iamjadhav/mobile_robot_arm/meshes/picking_arm.STL

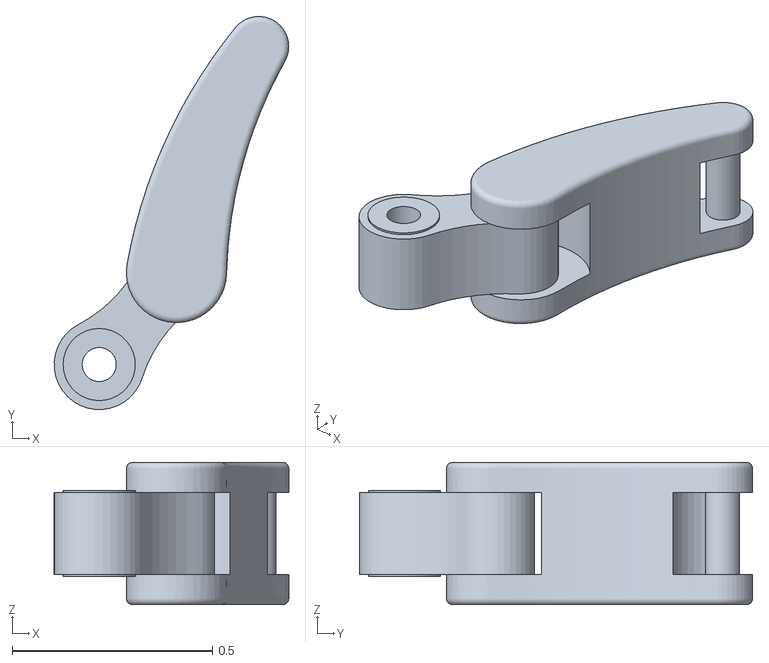
[picture p27: CAD file, 2021-12-11]
meshes/picking_arm.STL
0.585 x 0.981 x 0.355
