iamjadhav/mobile_robot_arm/solidworks_assembly/trolley.SLDPRT

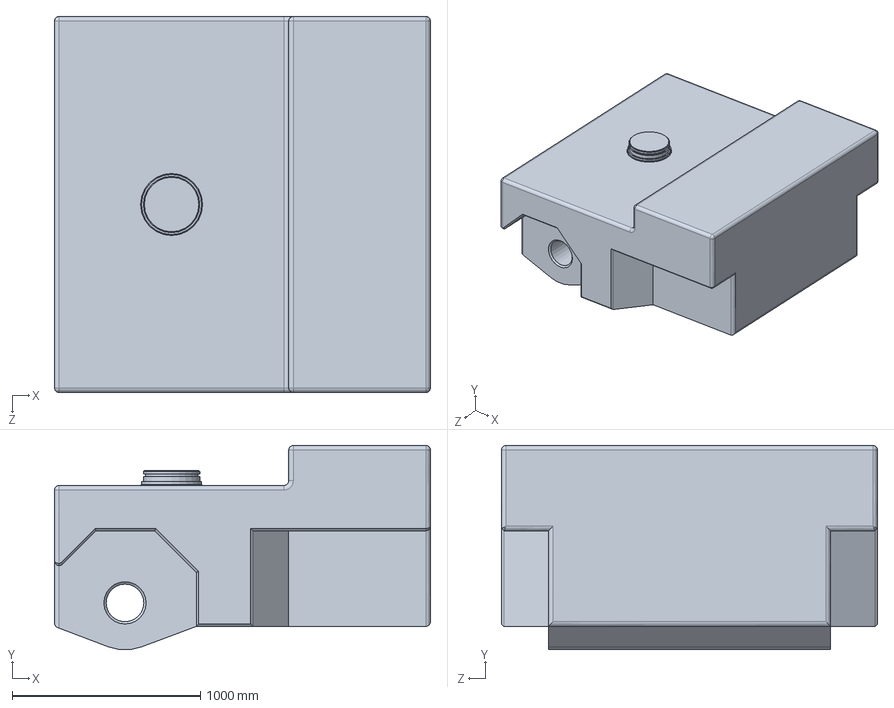
[picture p28: CAD file, 2021-12-11]
solidworks_assembly/trolley.SLDPRT
2000.0 x 1085.8 x 2000.0 mm
