iamjadhav/mobile_robot_arm/meshes/front_right_wheel.STL

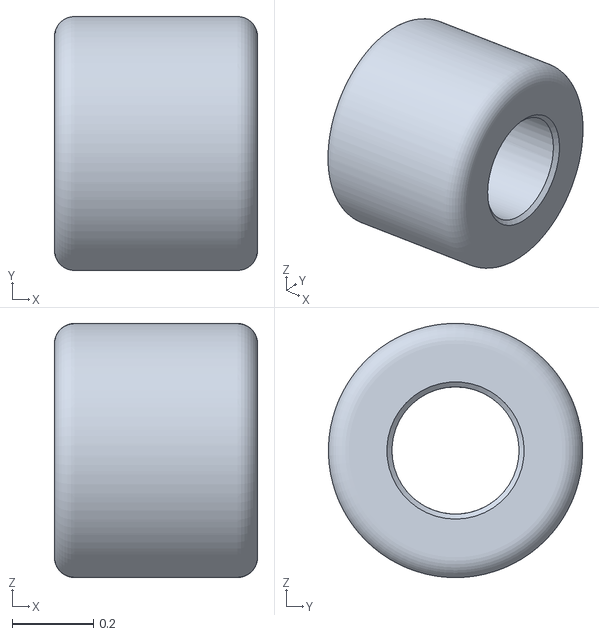
[picture p29: CAD file, 2021-12-11]
meshes/front_right_wheel.STL
0.5 x 0.625 x 0.625
