iamjadhav/mobile_robot_arm/solidworks_assembly/pivot.SLDPRT

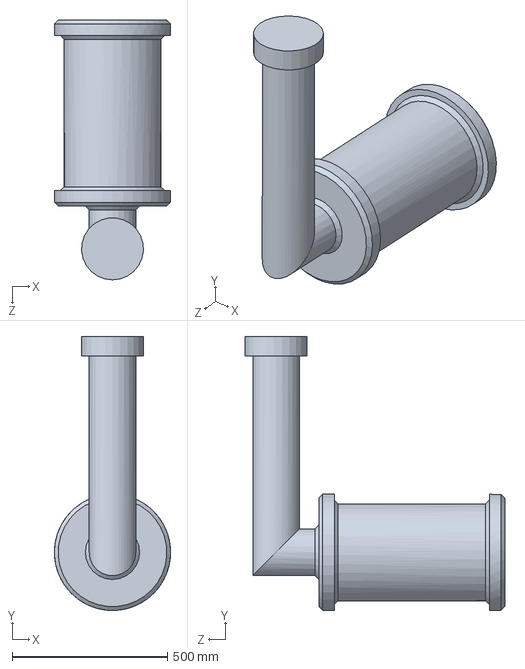
[picture p30: CAD file, 2021-12-11]
solidworks_assembly/pivot.SLDPRT
374.6 x 883.5 x 837.5 mm
