iamjadhav/mobile_robot_arm/solidworks_assembly/jaw_updated.SLDPRT

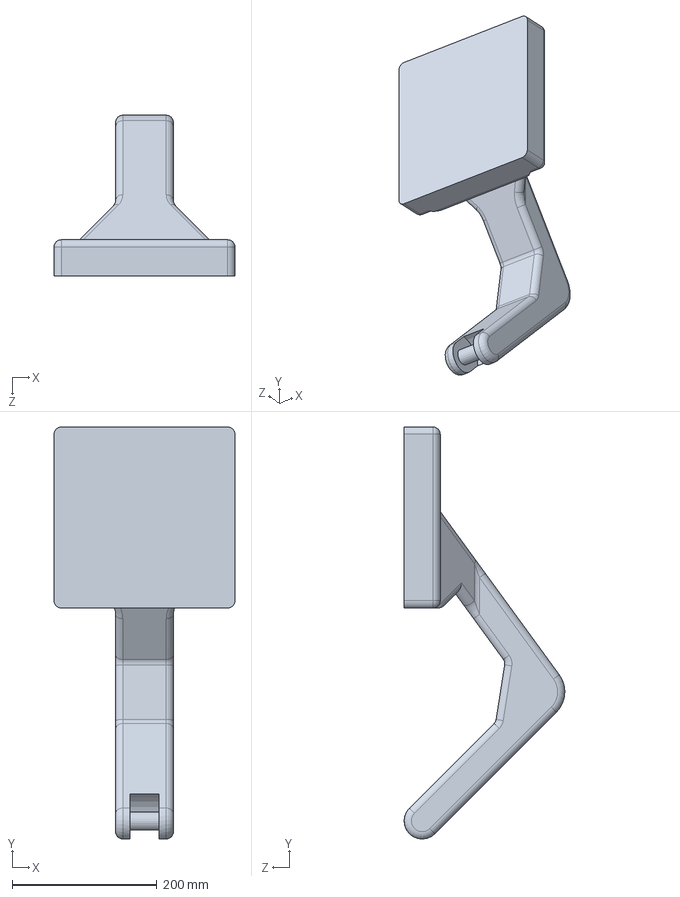
[picture p31: CAD file, 2021-12-11]
solidworks_assembly/jaw_updated.SLDPRT
250.0 x 569.2 x 222.1 mm
