iamjadhav/mobile_robot_arm/meshes/rotating_arm.STL

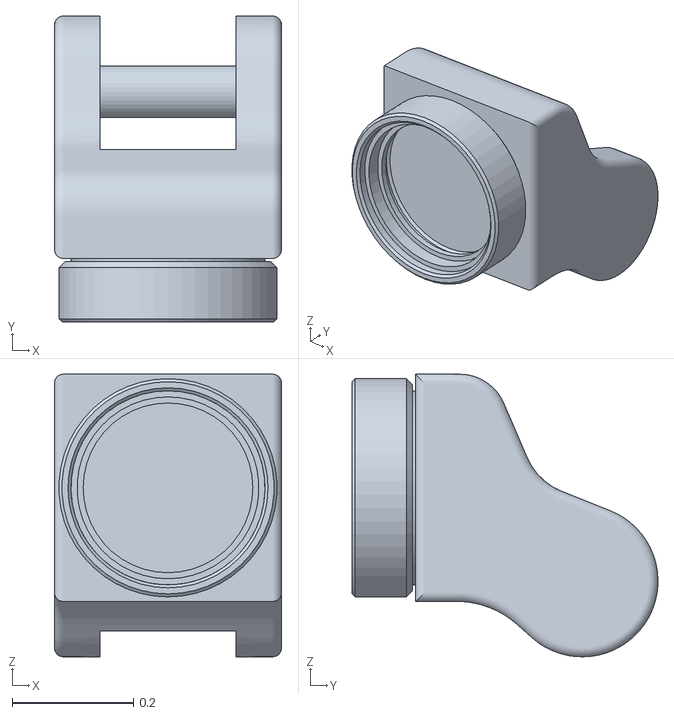
[picture p32: CAD file, 2021-12-11]
meshes/rotating_arm.STL
0.375 x 0.505 x 0.466
