iamjadhav/mobile_robot_arm/solidworks_assembly/rear_axle.SLDPRT

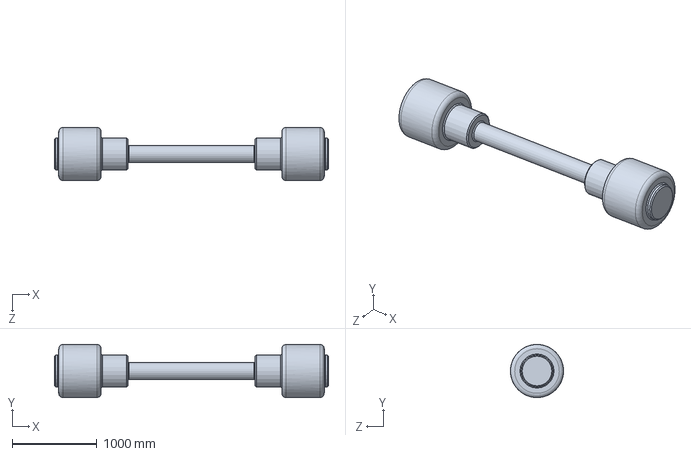
[picture p33: CAD file, 2021-12-11]
solidworks_assembly/rear_axle.SLDPRT
3225.0 x 625.0 x 624.5 mm
