iamjadhav/mobile_robot_arm/meshes/rear_transmission.STL

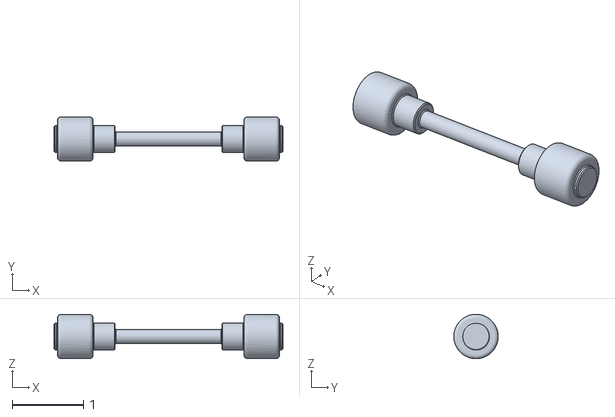
[picture p34: CAD file, 2021-12-11]
meshes/rear_transmission.STL
3.22 x 0.625 x 0.625
